Alt0183/Alt0183/docs/IMG/alt-0.jpg

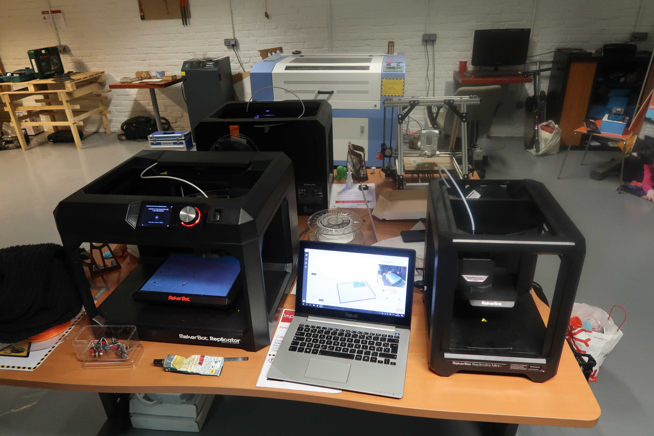
docs/IMG/alt-0.jpg
