Alt0183/Alt0183/docs/IMG/alt-3.jpg

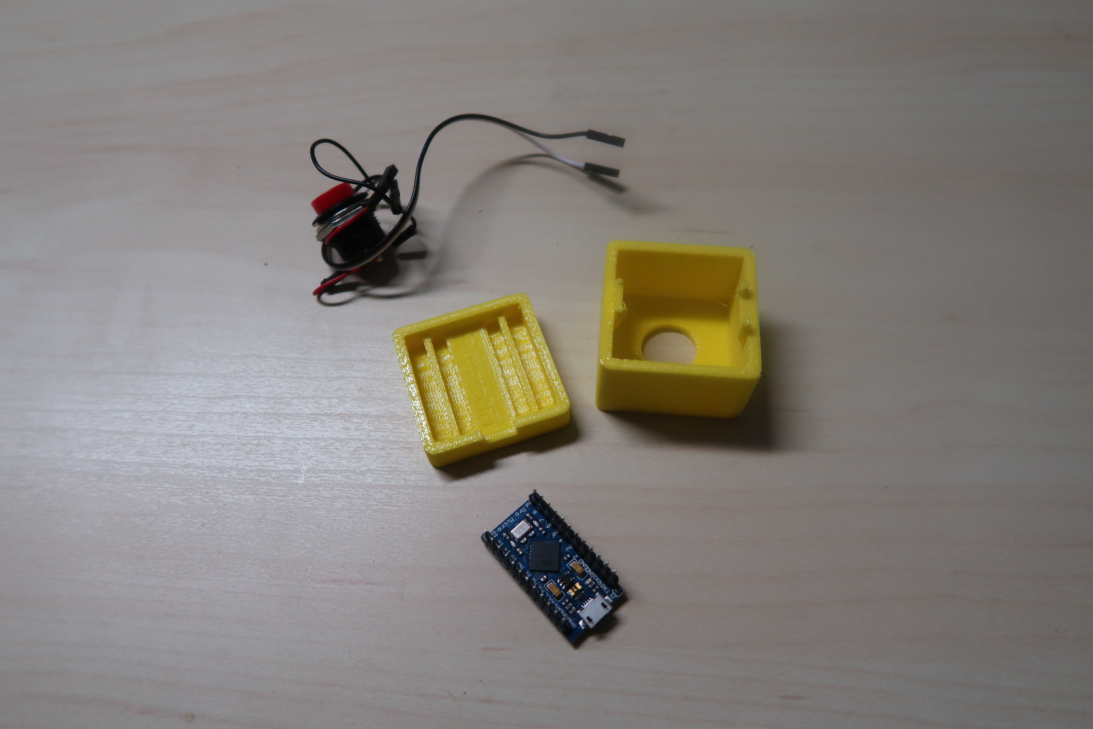
docs/IMG/alt-3.jpg
