Alt0183/Alt0183/docs/IMG/branchement.jpg

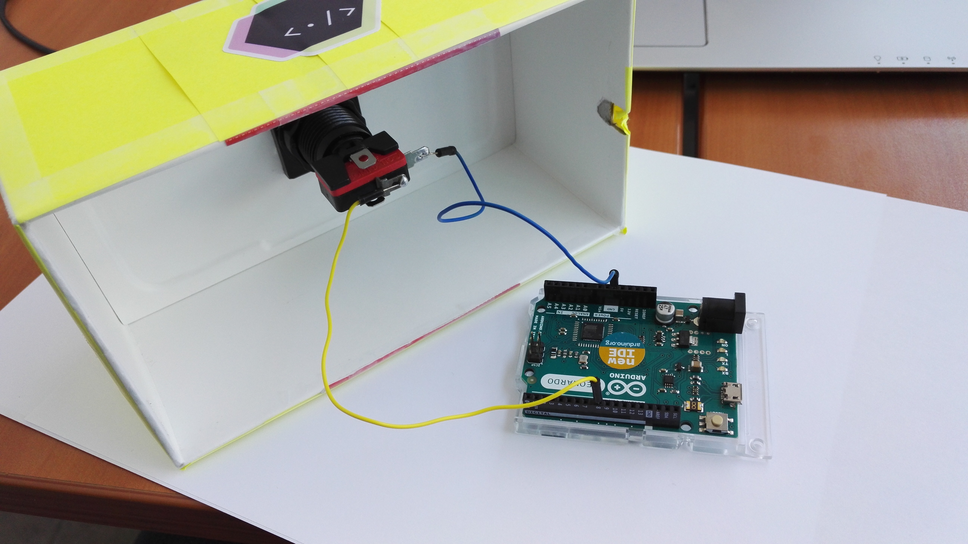
docs/IMG/branchement.jpg
