Alt0183/Alt0183/docs/IMG/buzzer.jpg

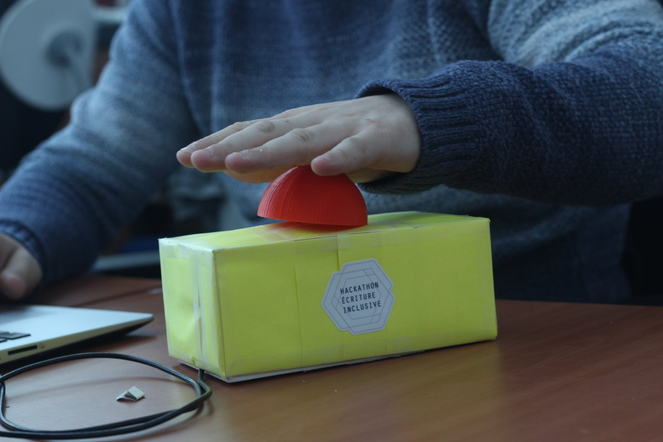
docs/IMG/buzzer.jpg
