Alt0183/Alt0183/docs/IMG/fin.jpg

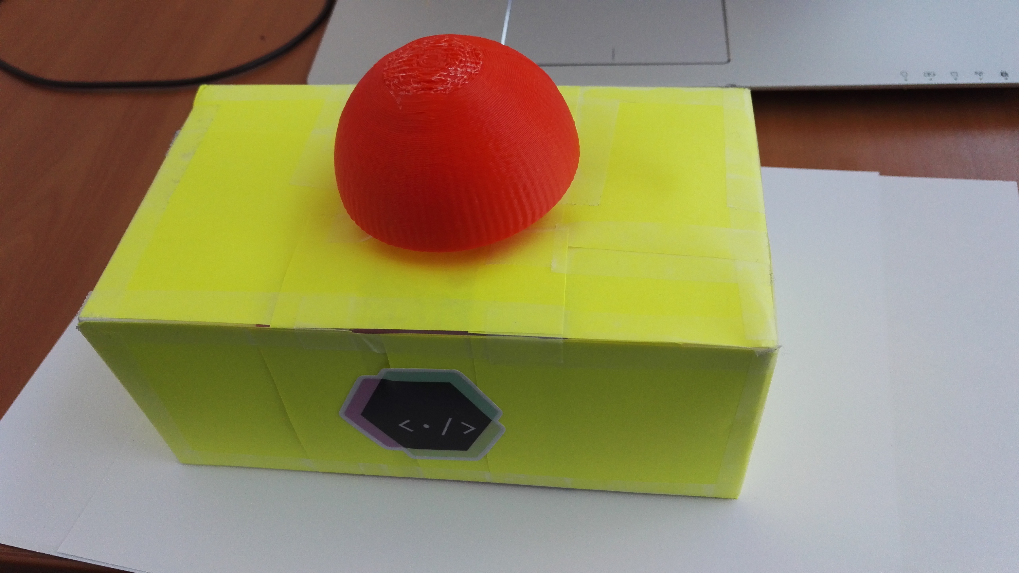
docs/IMG/fin.jpg
