Alt0183/Alt0183/docs/IMG/peinture.jpg

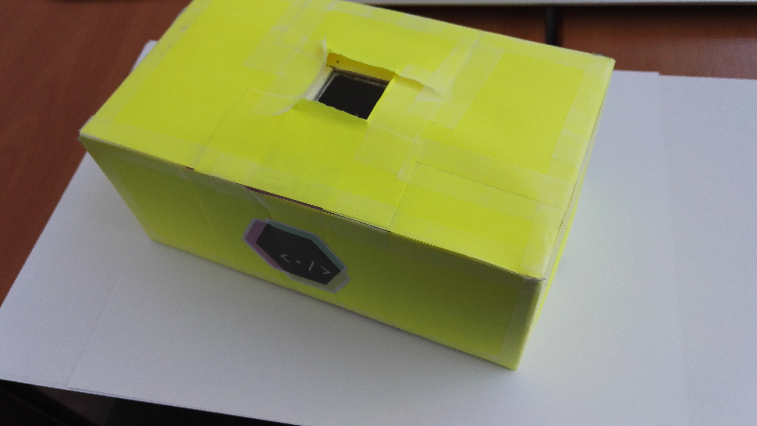
docs/IMG/peinture.jpg
