Alt0183/Alt0183/docs/IMG/percage.jpg

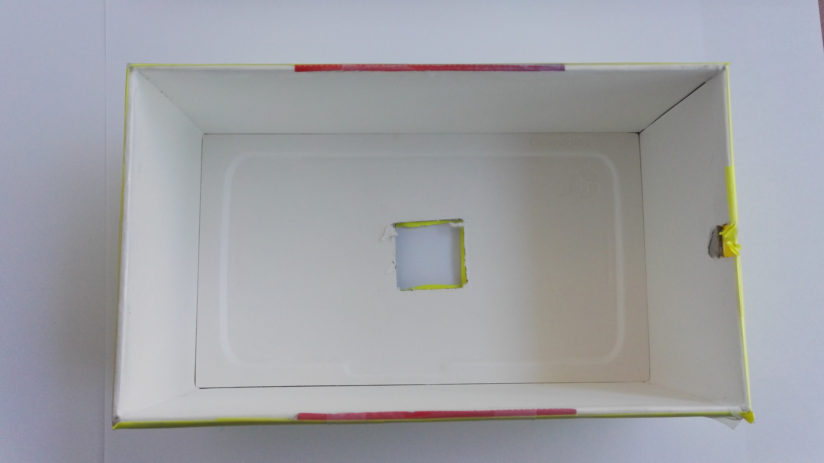
docs/IMG/percage.jpg
